thierry7100/PhotoBooth-1/firmware/1.png

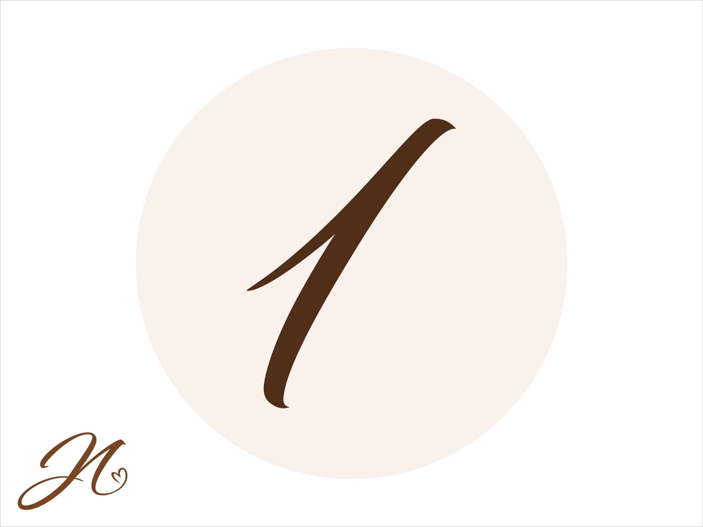
firmware/1.png
