thierry7100/PhotoBooth-1/firmware/2.png

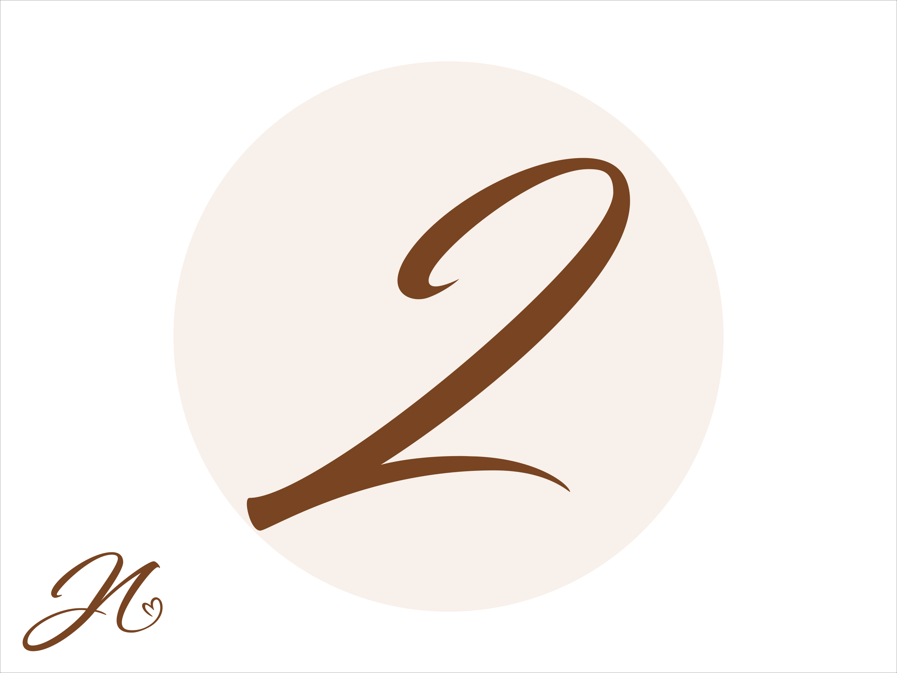
firmware/2.png
