thierry7100/PhotoBooth-1/firmware/3.png

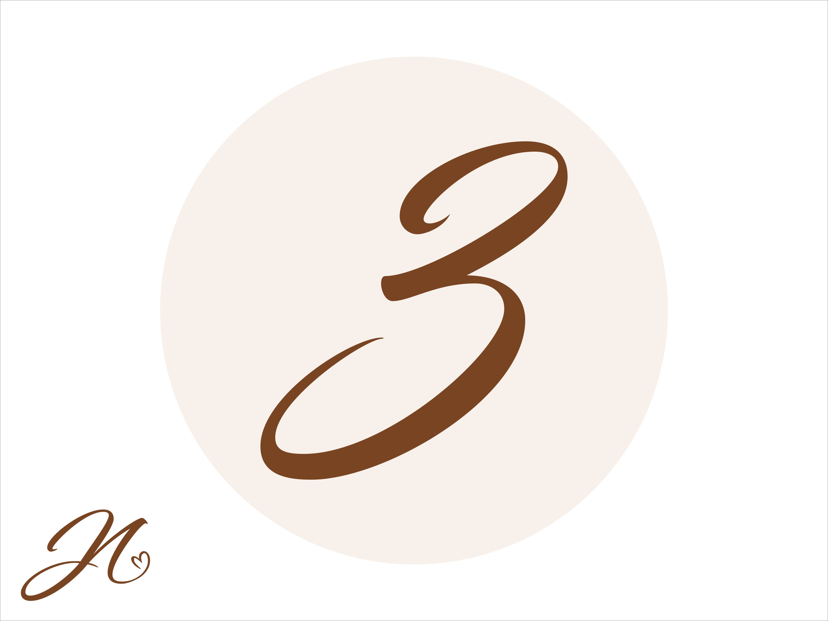
firmware/3.png
