thierry7100/PhotoBooth-1/firmware/Merci.png

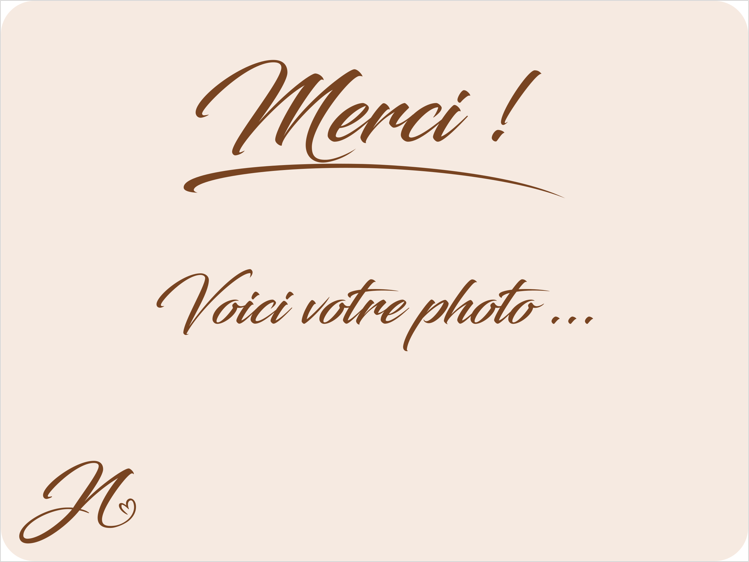
firmware/Merci.png
