thierry7100/PhotoBooth-1/hardware/pic/photo2.jpg

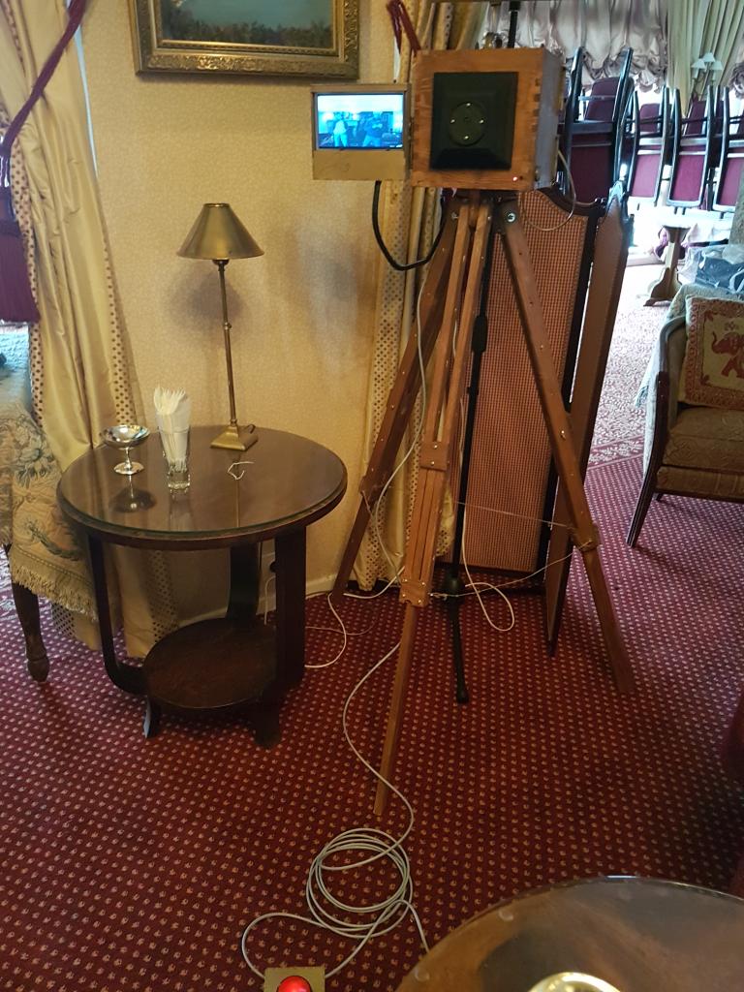
hardware/pic/photo2.jpg
